mathieulegoc/SmartTokens/material/tokenNotifier/img/folderfilled.png

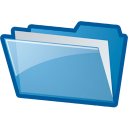
material/tokenNotifier/img/folderfilled.png
