mathieulegoc/SmartTokens/material/tokenNotifier/img/puck-x.png

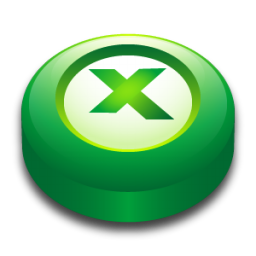
material/tokenNotifier/img/puck-x.png
