mathieulegoc/SmartTokens/material/tokenNotifier/img/3.png

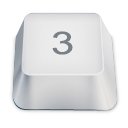
material/tokenNotifier/img/3.png
