mathieulegoc/SmartTokens/material/tokenNotifier/img/inbox.png

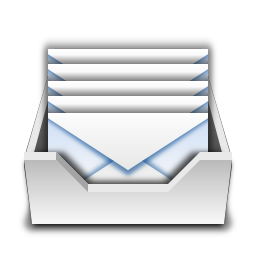
material/tokenNotifier/img/inbox.png
