mathieulegoc/SmartTokens/material/tokenNotifier/img/puck-x2.png

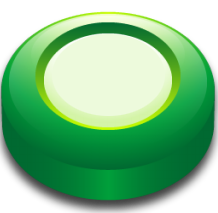
material/tokenNotifier/img/puck-x2.png
