mathieulegoc/SmartTokens/material/tokenNotifier/img/puck.png

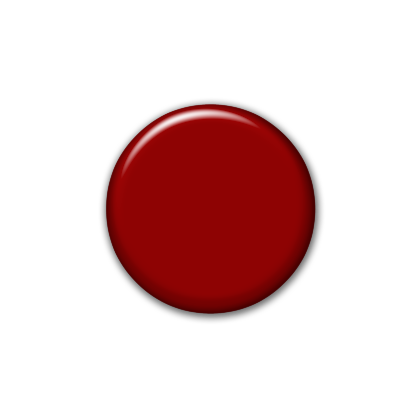
material/tokenNotifier/img/puck.png
