mathieulegoc/SmartTokens/material/Microcontrollers Program/Robots/qt1070.c

/******************************************************************************* 
*   $FILE:  QT_I2C.c
*   Brief: Application interfaces to drive the QT device 
*   Atmel Corporation:  http://www.atmel.com
*   Support email:  touch@atmel.com
******************************************************************************/
/*  License
*   Copyright (c) 2012, Atmel Corporation All rights reserved.
*   
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
*   3. The name of ATMEL may not be used to endorse or promote products derived
*   from this software without specific prior written permission.
*   
*   THIS SOFTWARE IS PROVIDED BY ATMEL "AS IS" AND ANY EXPRESS OR IMPLIED
*   WARRANTIES, INCLUDING, BUT NOT LIMITED TO, THE IMPLIED WARRANTIES OF
*   MERCHANTABILITY AND FITNESS FOR A PARTICULAR PURPOSE ARE EXPRESSLY AND
*   SPECIFICALLY DISCLAIMED. IN NO EVENT SHALL ATMEL BE LIABLE FOR ANY DIRECT,
*   INDIRECT, INCIDENTAL, SPECIAL, EXEMPLARY, OR CONSEQUENTIAL DAMAGES
*   (INCLUDING, BUT NOT LIMITED TO, PROCUREMENT OF SUBSTITUTE GOODS OR SERVICES;
*   LOSS OF USE, DATA, OR PROFITS; OR BUSINESS INTERRUPTION) HOWEVER CAUSED AND
*   ON ANY THEORY OF LIABILITY, WHETHER IN CONTRACT, STRICT LIABILITY, OR TORT
*   (INCLUDING NEGLIGENCE OR OTHERWISE) ARISING IN ANY WAY OUT OF THE USE OF
*   THIS SOFTWARE, EVEN IF ADVISED OF THE POSSIBILITY OF SUCH DAMAGE.
*/

/*============================================================================
Include files
============================================================================*/
#include "robot_functions.h"
#include "Timers.h"
#include <dbg.h>
#include <dbg_uart.h>
#include "I2C.h"
#include "qt1070.h"


/*============================================================================
Global variable definitions
============================================================================*/

// Setup block structure
SetupBlock setup_block;

// application storage for QT device-status
uint8 QtStatus[QT_STATUS_SIZE];

uint8 QTBuffer[22] = {0};

/*============================================================================
Function Definitions
============================================================================*/
/*============================================================================
Name    :   InitQtInterface
------------------------------------------------------------------------------
Purpose :	Initialize communication interface and change notification pin
			and reset pin
Input   :   none
Output  :   none
Return	:	none
Notes   :
============================================================================*/
PUBLIC void initQtInterface(void)
{
	setup_block.key0_NTHR=
	setup_block.key1_NTHR=
	setup_block.key2_NTHR=
	setup_block.key3_NTHR=
	setup_block.key4_NTHR=
	setup_block.key5_NTHR=
	setup_block.key6_NTHR=20;

	setup_block.key0_AVE_AKS=
	setup_block.key1_AVE_AKS=
	setup_block.key2_AVE_AKS=
	setup_block.key3_AVE_AKS=
	setup_block.key4_AVE_AKS=
	setup_block.key5_AVE_AKS=0x20;
	setup_block.key6_AVE_AKS=0;

	setup_block.key0_DI=
	setup_block.key1_DI=
	setup_block.key2_DI=
	setup_block.key3_DI=
	setup_block.key4_DI=
	setup_block.key5_DI=
	setup_block.key6_DI=4;

	setup_block.FastOutDI_MaxCal_GuardChannel = 0x17; //No guard

	setup_block.LP_Mode = 3; // 24ms between key measurements
	setup_block.Max_On_Dur = 180;

	if(getQTDeviceID()==QT_DEVICE_ID){
		vWaitMilliseconds(1);
		resetQT();
		vWaitMilliseconds(250);
		writeSetupBlock();
		vWaitMilliseconds(1);
		calibrateQT();
	}
}

/*============================================================================
Name    :   ReadSetupBlock
------------------------------------------------------------------------------
Purpose :	Read entire setup block from QT-device
Input   :   ReadLength	:	Number of bytes to read
			ReadPtr		:	Pointer to byte array for read-data
Output  :   none
Return	:	TRUE if read successful, else FALSE
Notes   :
============================================================================*/
PUBLIC bool readSetupBlock(uint8 ReadLength, uint8 *ReadPtr)
{
	// Read setup block
	return true;
}		

/*============================================================================
Name    :   WriteSetupBlock
------------------------------------------------------------------------------
Purpose :	write entire setup block to QT-device
Input   :   WriteLength	:	Number of bytes to write
			WritePtr	:	Pointer to byte array containing write-data
Output  :   none
Return	:	TRUE if write successful, else FALSE
Notes   :
============================================================================*/
PUBLIC bool writeSetupBlock()
{	
	bool b = writeBytes(QT_ADDRESS,QT_SETUPS_BLOCK_ADDR,sizeof(setup_block),(uint8*)&setup_block);
	vWaitMilliseconds(250);
	return b;
}

/*============================================================================
Name    :   ReadKeyStatus
------------------------------------------------------------------------------
Purpose :	Read detection status of all keys
Input   :   ReadLength	:	Number of bytes to read
			ReadPtr		:	Pointer to byte array for read-data
Output  :   none
Return	:	TRUE if read successful, else FALSE
Notes   :
============================================================================*/
PUBLIC uint8 readQTKeyStatus(void)
{
	// Read detection status of all keys
	readByte(QT_ADDRESS,QT_KEY_STATUS,QTBuffer);
	vWaitMicroseconds(50);
	return QTBuffer[0];
}

/*============================================================================
Name    :   ResetQT
------------------------------------------------------------------------------
Purpose :   Performs a hardware reset of the QT device
Input   :   none
Output  :   none
Return	:   none
Notes   :
============================================================================*/
PUBLIC void resetQT(void)
{
	writeByte(QT_ADDRESS, QT_RESET, 0xFF);
	vWaitMilliseconds(50);
}

/*============================================================================
Name    :   CalibrateQT
------------------------------------------------------------------------------
Purpose :   triggers the device to start a calibration cycle
Input   :   none
Output  :   none
Return	:   none
Notes   :
============================================================================*/
PUBLIC void calibrateQT(void)
{
	uint8 calibrating = 0;
	writeByte(QT_ADDRESS, QT_CALIBRATE, 0xFF);\
	do{
		vWaitMilliseconds(1);
		readBit(QT_ADDRESS,QT_DETECTION_STATUS,7,&calibrating);
	}while(calibrating>0);
	vWaitMilliseconds(1);
}

/*============================================================================
Name    :   getQTDeviceID
------------------------------------------------------------------------------
Purpose :   Check communication is ready and able to read Chip ID
Input   :   none
Output  :   none
Return	:   none
Notes   :
============================================================================*/
PUBLIC uint8 getQTDeviceID(void)
{
	readByte(QT_ADDRESS, QT_CHIP_ID, QTBuffer);
	vWaitMilliseconds(1);
	return QTBuffer[0];
}

/*============================================================================
Name    :   isQTDataReady
------------------------------------------------------------------------------
Purpose :   Check the TOUCCH_CHANGE pin to see if data is ready
Input   :   none
Output  :   none
Return	:   none
Notes   :
============================================================================*/
PUBLIC bool isQTDataReady(void)
{
	return ((u32AHI_DioReadInput()&ROBOT_TOUCH_CHANGE)==0);
}
