mathieulegoc/SmartTokens/material/Microcontrollers Program/Robots/qt1070.h

/*******************************************************************************
*   $FILE:  QT1070.h
*   Brief: Header file for the AT42QT1070 device and it consists AT42QT1070 
*           Setup Block structure and address map enums
*   Atmel Corporation:  http:/www.atmel.com
*   Support email:  touch@atmel.com
******************************************************************************/
/*  License
*   Copyright (c) 2012, Atmel Corporation All rights reserved.
*
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
*   3. The name of ATMEL may not be used to endorse or promote products derived
*   from this software without specific prior written permission.
*
*   THIS SOFTWARE IS PROVIDED BY ATMEL "AS IS" AND ANY EXPRESS OR IMPLIED
*   WARRANTIES, INCLUDING, BUT NOT LIMITED TO, THE IMPLIED WARRANTIES OF
*   MERCHANTABILITY AND FITNESS FOR A PARTICULAR PURPOSE ARE EXPRESSLY AND
*   SPECIFICALLY DISCLAIMED. IN NO EVENT SHALL ATMEL BE LIABLE FOR ANY DIRECT,
*   INDIRECT, INCIDENTAL, SPECIAL, EXEMPLARY, OR CONSEQUENTIAL DAMAGES
*   (INCLUDING, BUT NOT LIMITED TO, PROCUREMENT OF SUBSTITUTE GOODS OR SERVICES;
*   LOSS OF USE, DATA, OR PROFITS; OR BUSINESS INTERRUPTION) HOWEVER CAUSED AND
*   ON ANY THEORY OF LIABILITY, WHETHER IN CONTRACT, STRICT LIABILITY, OR TORT
*   (INCLUDING NEGLIGENCE OR OTHERWISE) ARISING IN ANY WAY OUT OF THE USE OF
*   THIS SOFTWARE, EVEN IF ADVISED OF THE POSSIBILITY OF SUCH DAMAGE.
*/

#ifndef _QT1070_H_
#define _QT1070_H_

/*============================================================================
Include files
============================================================================*/
#include <jendefs.h>
#include <AppHardwareApi.h>
#include "Config.h"
#include "robot_functions.h"

/*============================================================================
Macros
============================================================================*/

// Chip ID (read from device-address 0)
#define QT_DEVICE_ID	0x2E

// I2C address	
#define QT_ADDRESS		0x1B

// Setup block start address
#define QT_SETUPS_BLOCK_ADDR	32

// detection status and key status start address
#define QT_STATUS_ADDR	2

/* 
application storage for QT1070 device-status

QtStatus[0] - Detection Status 
				Bit0 - TOUCH : This bit is set if any keys are in detect.
				Bit6 - OVERFLOW : This bit is set if the time to acquire all 
                key signals exceeds 8ms
				bit7 - CALIBRATE : This bit is set during a calibrate sequence
				
QtStatus[1] - Key Status 
				bits 0 - 6 : Indicates which keys are in detection 
                  (Touched keys report as 1) 
*/

// QtStatus array size
#define QT_STATUS_SIZE	2

/*============================================================================
Enums
============================================================================*/
/* 
 * This address map can be used for read\write particular info from QT device
 * using the interfaces twi_read() or twi_write()
 */

enum { // QT1070 registers
	QT_CHIP_ID = 0,
	QT_FIRMWARE_VERSION = 1,
	QT_DETECTION_STATUS = 2,
	QT_KEY_STATUS = 3,
	QT_KEY0_SIGNAL = 4,
	QT_KEY1_SIGNAL = 6,
	QT_KEY2_SIGNAL = 8,
	QT_KEY3_SIGNAL = 10,
	QT_KEY4_SIGNAL = 12,
	QT_KEY5_SIGNAL = 14,
	QT_KEY6_SIGNAL = 16,
	QT_KEY0_REFERENCE = 18,
	QT_KEY1_REFERENCE = 20,
	QT_KEY2_REFERENCE = 22,
	QT_KEY3_REFERENCE = 24,
	QT_KEY4_REFERENCE = 26,
	QT_KEY5_REFERENCE = 28,
	QT_KEY6_REFERENCE = 30,
	QT_KEY0_NTHR = 32,
	QT_KEY1_NTHR = 33,
	QT_KEY2_NTHR = 34,
	QT_KEY3_NTHR = 35,
	QT_KEY4_NTHR = 36,
	QT_KEY5_NTHR = 37,
	QT_KEY6_NTHR = 38,
	QT_KEY0__AVE_AKS = 39,
	QT_KEY1_AVE_AKS = 40,
	QT_KEY2_AVE_AKS = 41,
	QT_KEY3_AVE_AKS = 42,
	QT_KEY4_AVE_AKS = 43,
	QT_KEY5_AVE_AKS = 44,
	QT_KEY6_AVE_AKS = 45,
	QT_KEY0_DI = 46,
	QT_KEY1_DI = 47,
	QT_KEY2_DI = 48,
	QT_KEY3_DI = 49,
	QT_KEY4_DI = 50,
	QT_KEY5_DI = 51,
	QT_KEY6_DI = 52,
	QT_FO_MO_GDNO = 53,
	QT_LP = 54,
	QT_MAX_ON_DURATION = 55,
	QT_CALIBRATE = 56,
	QT_RESET = 57,
}QTRegisters;

/*============================================================================
Type definitions
============================================================================*/

typedef struct
{
	// Negative Threshold(NTHR)	
	uint8 key0_NTHR;  // Key0 Negative Threshold
	uint8 key1_NTHR;  // Key1 Negative Threshold
	uint8 key2_NTHR;  // Key2 Negative Threshold
	uint8 key3_NTHR;  // Key3 Negative Threshold
	uint8 key4_NTHR;  // Key4 Negative Threshold
	uint8 key5_NTHR;  // Key5 Negative Threshold
	uint8 key6_NTHR;  // Key6 Negative Threshold
	
	// Averaging factor(AVE)/Adjucent key suppression level(AKS)	
	uint8 key0_AVE_AKS;  // Key0 AKS group
	uint8 key1_AVE_AKS;  // Key1 AKS group
	uint8 key2_AVE_AKS;  // Key2 AKS group
	uint8 key3_AVE_AKS;  // Key3 AKS group
	uint8 key4_AVE_AKS;  // Key4 AKS group
	uint8 key5_AVE_AKS;  // Key5 AKS group
	uint8 key6_AVE_AKS;  // Key6 AKS group
	
	// Detection Integrator(DI)	
	int8 key0_DI;  // Key0 Detection Integrator counter
	int8 key1_DI;  // Key1 Detection Integrator counter
	int8 key2_DI;  // Key2 Detection Integrator counter
	int8 key3_DI;  // Key3 Detection Integrator counter
	int8 key4_DI;  // Key4 Detection Integrator counter
	int8 key5_DI;  // Key5 Detection Integrator counter
	int8 key6_DI;  // Key6 Detection Integrator counter
	
	// Fast out DI, max cal, Guard channel	
	uint8 FastOutDI_MaxCal_GuardChannel;
	// 8ms intervals between key measurements	
	uint8 LP_Mode;

	// Max On Duaration
	uint8 Max_On_Dur;
	
}SetupBlock;

/*============================================================================
External variables
============================================================================*/
extern SetupBlock setup_block;
extern uint8 QtStatus[2];

/*============================================================================
Prototypes
============================================================================*/
PUBLIC void initQtInterface(void);
PUBLIC bool readSetupBlock(uint8 ReadLength, uint8 *ReadPtr);
PUBLIC bool writeSetupBlock();
PUBLIC uint8 readQTKeyStatus(void);
PUBLIC void resetQT(void);
PUBLIC uint8 getQTDeviceID(void);
PUBLIC void calibrateQT(void);
PUBLIC bool isQTDataReady(void);
#endif /* _QT1070_H_ */
/*============================================================================
  END OF FILE 
============================================================================*/						 
					 
