mathieulegoc/SmartTokens/material/Microcontrollers Program/Common/Source/Timers.h

#ifndef _TIMERS_H_
#define _TIMERS_H_

/*============================================================================
Include files
============================================================================*/
#include <jendefs.h>
#include <AppHardwareApi.h>
#include "Config.h"

/*============================================================================
Macros
============================================================================*/


/*============================================================================
Enums
============================================================================*/


/*============================================================================
Type definitions
============================================================================*/


/*============================================================================
External variables
============================================================================*/


/*============================================================================
Prototypes
============================================================================*/
PUBLIC void vWaitMilliseconds(uint16 milliseconds);
PUBLIC void vWaitMicroseconds(uint16 microseconds);
#endif /* _TIMERS_H_ */
/*============================================================================
  END OF FILE
============================================================================*/
